terriblefire/tfmsx/testsuite/rtl/PULLUP.v

// $Header: /devl/xcs/repo/env/Databases/CAEInterfaces/verunilibs/data/unisims/PULLUP.v,v 1.5 2007/05/23 21:43:44 patrickp Exp $
///////////////////////////////////////////////////////////////////////////////
// Copyright (c) 1995/2004 Xilinx, Inc.
// All Right Reserved.
///////////////////////////////////////////////////////////////////////////////
//   ____  ____
//  /   /\/   /
// /___/  \  /    Vendor : Xilinx
// \   \   \/     Version : 10.1
//  \   \         Description : Xilinx Functional Simulation Library Component
//  /   /                  Resistor to VCC
// /___/   /\     Filename : PULLUP.v
// \   \  /  \    Timestamp : Thu Mar 25 16:43:32 PST 2004
//  \___\/\___\
//
// Revision:
//    03/23/04 - Initial version.
//    05/23/07 - Changed timescale to 1 ps / 1 ps.
//    05/23/07 - Added wire declaration for internal signals.

`timescale  1 ps / 1 ps


`celldefine

module PULLUP (O);


`ifdef XIL_TIMING

    parameter LOC = "UNPLACED";

`endif

  
    output O;

    wire A;

    pullup (A);
    buf (weak0,weak1) #(100,100) (O,A);

endmodule

`endcelldefine
