terriblefire/tfmsx/testsuite/rtl/cells_sim.v

`timescale 1ns / 1ps

module SB_GB (
	input  USER_SIGNAL_TO_GLOBAL_BUFFER,
	output GLOBAL_BUFFER_OUTPUT
);
	assign GLOBAL_BUFFER_OUTPUT = USER_SIGNAL_TO_GLOBAL_BUFFER;
endmodule

/* verilator lint_off UNUSED */
/* verilator lint_off UNDRIVEN */
(* blackbox *)
module SB_PLL40_2F_PAD (
	input   PACKAGEPIN,
	output  PLLOUTCOREA,
	output  PLLOUTGLOBALA,
	output  PLLOUTCOREB,
	output  PLLOUTGLOBALB,
	input   EXTFEEDBACK,
	input   [7:0] DYNAMICDELAY,
	output reg LOCK = 1'b1,
	input   BYPASS,
	input   RESETB,
	input   LATCHINPUTVALUE,
	output  SDO,
	input   SDI,
	input   SCLK
);
	parameter FEEDBACK_PATH = "SIMPLE";
	parameter DELAY_ADJUSTMENT_MODE_FEEDBACK = "FIXED";
	parameter DELAY_ADJUSTMENT_MODE_RELATIVE = "FIXED";
	parameter SHIFTREG_DIV_MODE = 2'b00;
	parameter FDA_FEEDBACK = 4'b0000;
	parameter FDA_RELATIVE = 4'b0000;
	parameter PLLOUT_SELECT_PORTA = "GENCLK";
	parameter PLLOUT_SELECT_PORTB = "GENCLK";
	parameter DIVR = 4'b0000;
	parameter DIVF = 7'b0000000;
	parameter DIVQ = 3'b000;
	parameter FILTER_RANGE = 3'b000;
	parameter ENABLE_ICEGATE_PORTA = 1'b0;
	parameter ENABLE_ICEGATE_PORTB = 1'b0;
	parameter TEST_MODE = 1'b0;
	parameter EXTERNAL_DIVIDE_FACTOR = 1;

`include "../clocks.vinc"

endmodule
/* verilator lint_on UNUSED */
/* verilator lint_on UNDRIVEN */
